idpromnut/usb-keyboard/docs/IBM-ModelM-101/DSC_9298.jpg

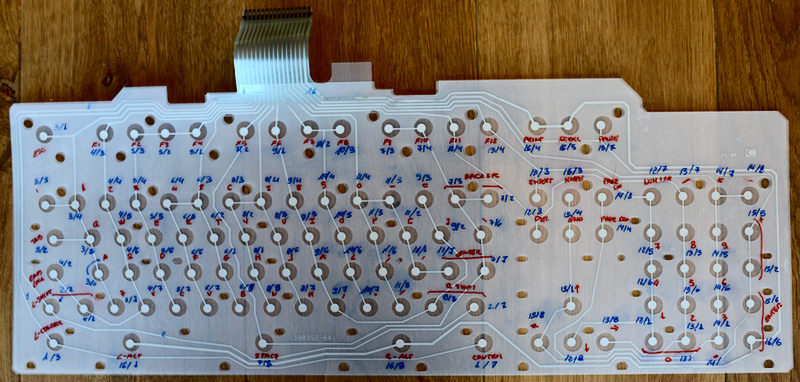
docs/IBM-ModelM-101/DSC_9298.jpg
