idpromnut/usb-keyboard/docs/IBM-ModelM-101/DSC_9300.jpg

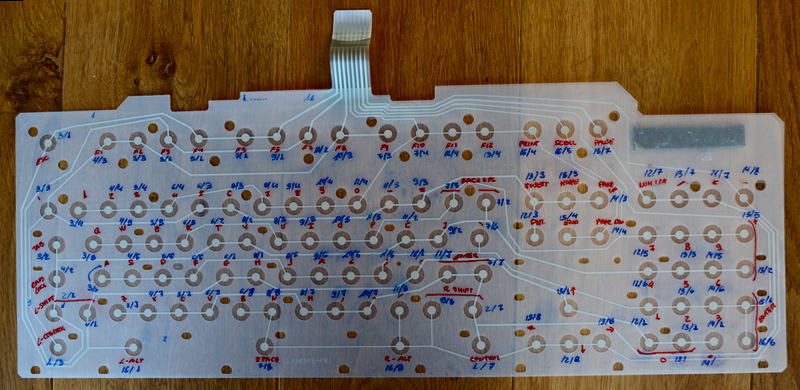
docs/IBM-ModelM-101/DSC_9300.jpg
