idpromnut/usb-keyboard/firmware/Core/Src/user_interface.c

#include "user_interface.h"
#include "main.h"
#include "stm32f1xx_hal.h"


void UserInterface_Init(void)
{
	UserInterface_Led_All_Off();
}


void UserInterface_Led_On(UserInterface_LedType led)
{
	if (led == CAPS_LOCK)
	{
		HAL_GPIO_WritePin(CAPS_LOCK_LED_GPIO_Port, CAPS_LOCK_LED_Pin, GPIO_PIN_RESET);
	}
	else if (led == SCROLL_LOCK)
	{
		HAL_GPIO_WritePin(SCROLL_LOCK_LED_GPIO_Port, SCROLL_LOCK_LED_Pin, GPIO_PIN_RESET);
	}
	else if (led == NUM_LOCK)
	{
		HAL_GPIO_WritePin(NUM_LOCK_LED_GPIO_Port, NUM_LOCK_LED_Pin, GPIO_PIN_RESET);
	}
}

void UserInterface_Led_Off(UserInterface_LedType led)
{
	if (led == CAPS_LOCK)
	{
		HAL_GPIO_WritePin(CAPS_LOCK_LED_GPIO_Port, CAPS_LOCK_LED_Pin, GPIO_PIN_SET);
	}
	else if (led == SCROLL_LOCK)
	{
		HAL_GPIO_WritePin(SCROLL_LOCK_LED_GPIO_Port, SCROLL_LOCK_LED_Pin, GPIO_PIN_SET);
	}
	else if (led == NUM_LOCK)
	{
		HAL_GPIO_WritePin(NUM_LOCK_LED_GPIO_Port, NUM_LOCK_LED_Pin, GPIO_PIN_SET);
	}
}


void UserInterface_Led_All_Off()
{
	UserInterface_Led_Off(CAPS_LOCK);
	UserInterface_Led_Off(SCROLL_LOCK);
	UserInterface_Led_Off(NUM_LOCK);
}

void UserInterface_Led_Set(UserInterface_LedType led, uint8_t state)
{
	if (state == 0)
	{
		UserInterface_Led_Off(led);
	}
	else
	{
		UserInterface_Led_On(led);
	}
}
